bmanga/rtep2019_team18/tools/QtGAITGui/MainWindow.cpp

#include "MainWindow.hpp"
#include "CalibrateWindow.hpp"
#include "FinalWindow.hpp"
#include "Training_mode.hpp"
#include "WelcomeWindow.hpp"
#include "intro_window.hpp"

MainWindow::MainWindow()
{
  auto *welcomeScreen = new WelcomeWindow();
  setCentralWidget(welcomeScreen);
  connect(welcomeScreen, &WindowBase::windowDone, this,
          &MainWindow::onWindowDone);

  m_client.set_message_handler(
      [this](const void *data, long len) { this->on_message(data, len); });
}

void MainWindow::onWindowDone(WindowKind wk, int extra)
{
  delete this->centralWidget();
  WindowBase *nextWindow = nullptr;
  switch (wk) {
    case WindowKind::Welcome:
      nextWindow = new IntroWindow();
      break;
    case WindowKind::Intro:
      nextWindow = new CalibrateWindow(extra, this);
      break;
    case WindowKind::Cal:
      if (extra == 0) {
        nextWindow = new TrainingMode<ProgressBar>(R"(
                                                   <html>
                                                   <center><b>Welcome to the Weight Shifting exercise!</b> <\center>
                                                   <br>
                                                   <br>
                                                   Shift your weight from one foot to the other to reach the target levels shown on each bar
                                                   <br>
                                                   </html>)",
                                                   this);
        ;
      }
      else {
        nextWindow = new TrainingMode<CircleWidget>(R"(
                                                    <html>
                                                    <center><b>Welcome to the Calf Pushes exercise!</b> <\center>
                                                    <br>
                                                    <br>
                                                    Shift your weight from heel to toes to  reach the target levels shown on each bar
                                                    <br>
                                                    </html>)",
                                                    this);
        ;
      }

      break;
  }
  connect(nextWindow, &WindowBase::windowDone, this, &MainWindow::onWindowDone);
  this->setCentralWidget(nextWindow);
}

MainWindow::~MainWindow() {}

void MainWindow::on_message(const void *d, long len)
{
  sensors_data data = {};
  memcpy(&data, d, sizeof(data));

  emit newFSRDataL(data.left);
  emit newFSRDataR(data.right);
}

void MainWindow::setCalibrationMax(double maxValue)
{
  calibrationMax = maxValue;
}
