bmanga/rtep2019_team18/tools/QtGAITGui/Training_mode.cpp

#include "Training_mode.hpp"
#include <QCheckBox>
#include <QDebug>
#include <QHBoxLayout>
#include <QLabel>
#include <QLineEdit>
#include <QPainter>
#include <QPushButton>
#include <QSplineSeries>
#include <QtCharts/QChartView>
#include <QtWidgets/QApplication>
#include <QtWidgets/QMainWindow>
#include "CircleWidget.hpp"
#include "Level_weight_shifting.hpp"
#include "progressbar.hpp"
