bmanga/rtep2019_team18/tools/QtGAITGui/WindowBase.hpp

#pragma once

#include <QWidget>

enum WindowKind {
  Welcome,
  Intro,
  Cal,
  Training,
  Final,
};

class WindowBase : public QWidget {
  Q_OBJECT
 public:
  WindowBase(QWidget *parent = nullptr) : QWidget(parent) {}
 signals:
  void windowDone(WindowKind, int);
};
