bmanga/rtep2019_team18/tools/QtGAITGui/intro_window.hpp

//
//  intro_window.hpp
//  rtep_team18
//
//  Created by Luca Rosalia on 07/04/2019.
//

#ifndef intro_window_hpp
#define intro_window_hpp

#include <stdio.h>
#include <QLabel>
#include <QPushButton>
#include <QtWidgets/QMainWindow>
#include "WindowBase.hpp"

class IntroWindow : public WindowBase {
 public:
  IntroWindow();
  ~IntroWindow();

  QPushButton *WSButton;
  QPushButton *CPButton;

 private slots:
  void onWSButtonPushed();
  void onCPButtonPushed();

 private:
  QLabel *Message;
};

#endif /* intro_window_hpp */
